HanRabbit/E-Cube/ECube/Firmware/ECube/src/ui.h

// SquareLine LVGL GENERATED FILE
// EDITOR VERSION: SquareLine Studio 1.0.5
// LVGL VERSION: 8.2
// PROJECT: ECubeUI

#ifndef _ECUBEUI_UI_H
#define _ECUBEUI_UI_H

#ifdef __cplusplus
extern "C" {
#endif

#if __has_include("lvgl.h")
#include "lvgl.h"
#else
#include "lvgl/lvgl.h"
#endif

extern lv_obj_t * ui_Screen1;
extern lv_obj_t * ui_Image1;
extern lv_obj_t * ui_Bar1;
extern lv_obj_t * ui_Label1;
extern lv_obj_t * ui_Label2;
extern lv_obj_t * ui_Screen2;
extern lv_obj_t * ui_Roller2;
extern lv_obj_t * ui_Label9;
extern lv_obj_t * ui_Button4;
extern lv_obj_t * ui_Label8;
extern lv_obj_t * ui_Screen3;
extern lv_obj_t * ui_Label3;
extern lv_obj_t * ui_Bar2;
extern lv_obj_t * ui_TextArea1;
extern lv_obj_t * ui_Keyboard1;
extern lv_obj_t * ui_Button3;
extern lv_obj_t * ui_Label12;
extern lv_obj_t * ui_Screen4;
extern lv_obj_t * ui_Bar3;
extern lv_obj_t * ui_Panel1;
extern lv_obj_t * ui_Label7;
extern lv_obj_t * ui_Label6;
extern lv_obj_t * ui_Label5;
extern lv_obj_t * ui_Label4;
extern lv_obj_t * ui_Button1;
extern lv_obj_t * ui_Label10;
extern lv_obj_t * ui_Button2;
extern lv_obj_t * ui_Label11;
extern lv_obj_t * ui_Screen5;
extern lv_obj_t * ui_Panel2;
extern lv_obj_t * ui_Label14;
extern lv_obj_t * ui_Roller1;
extern lv_obj_t * ui_Label13;
extern lv_obj_t * ui_Label16;
extern lv_obj_t * ui_Label15;
extern lv_obj_t * ui_Label26;
extern lv_obj_t * ui_Label27;
extern lv_obj_t * ui_Screen6;
extern lv_obj_t * ui_Label17;
extern lv_obj_t * ui_Dropdown1;
extern lv_obj_t * ui_Panel5;
extern lv_obj_t * ui_Label22;
extern lv_obj_t * ui_Label23;
extern lv_obj_t * ui_Panel4;
extern lv_obj_t * ui_Label20;
extern lv_obj_t * ui_Label21;
extern lv_obj_t * ui_Panel3;
extern lv_obj_t * ui_Label18;
extern lv_obj_t * ui_Label19;
extern lv_obj_t * ui_Panel6;
extern lv_obj_t * ui_Label24;
extern lv_obj_t * ui_Label25;

void ssid_scan(lv_event_t * e);
void selectWiFi(lv_event_t * e);
void ssid_scan(lv_event_t * e);
void PWD_input(lv_event_t * e);
void wifi_ref(lv_event_t * e);
void wifi_connect(lv_event_t * e);
void wifi_ref(lv_event_t * e);
void home_on_load(lv_event_t * e);
void time_switch_screen(lv_event_t * e);
void time_switch_screen(lv_event_t * e);
void selectArea(lv_event_t * e);

LV_IMG_DECLARE(ui_img_logo2_small_png);    // assets\Logo2_small.png




// void ui_init(void);

#ifdef __cplusplus
} /*extern "C"*/
#endif

#endif
