HanRabbit/E-Cube/ECube/Firmware/ECube/src/ui_events.c

// SquareLine LVGL GENERATED FILE
// EDITOR VERSION: SquareLine Studio 1.0.5
// LVGL VERSION: 8.2
// PROJECT: ECubeUI

#include "ui.h"



// void SSID_input(lv_event_t * e)
// {
// 	// Your code here
// }

// void wifi_connect(lv_event_t * e)
// {
// 	// Your code here
// }

// void ssid_scan(lv_event_t * e)
// {
// 	// Your code here
// }



// void selectWiFi(lv_event_t * e)
// {
// 	// Your code here
// }

// void PWD_input(lv_event_t * e)
// {
// 	// Your code here
// }

// void WiFiButtonDefocused(lv_event_t * e)
// {
// 	// Your code here
// }

// void wifi_ref(lv_event_t * e)
// {
// 	// Your code here
// }

// void wifi_ssid_scan(lv_event_t * e)
// {
// 	// Your code here
// }

// void home_on_load(lv_event_t * e)
// {
// 	// Your code here
// }

// void time_switch_screen(lv_event_t * e)
// {
// 	// Your code here
// }

// void virus_scr_click(lv_event_t * e)
// {
// 	// Your code here
// }

// void selectArea(lv_event_t * e)
// {
// 	// Your code here
// }
